ThomasRinsma/kb1/hardware/kb1.kicad_sch

## KiCad design hardware/kb1.kicad_sch (2024-02-07)

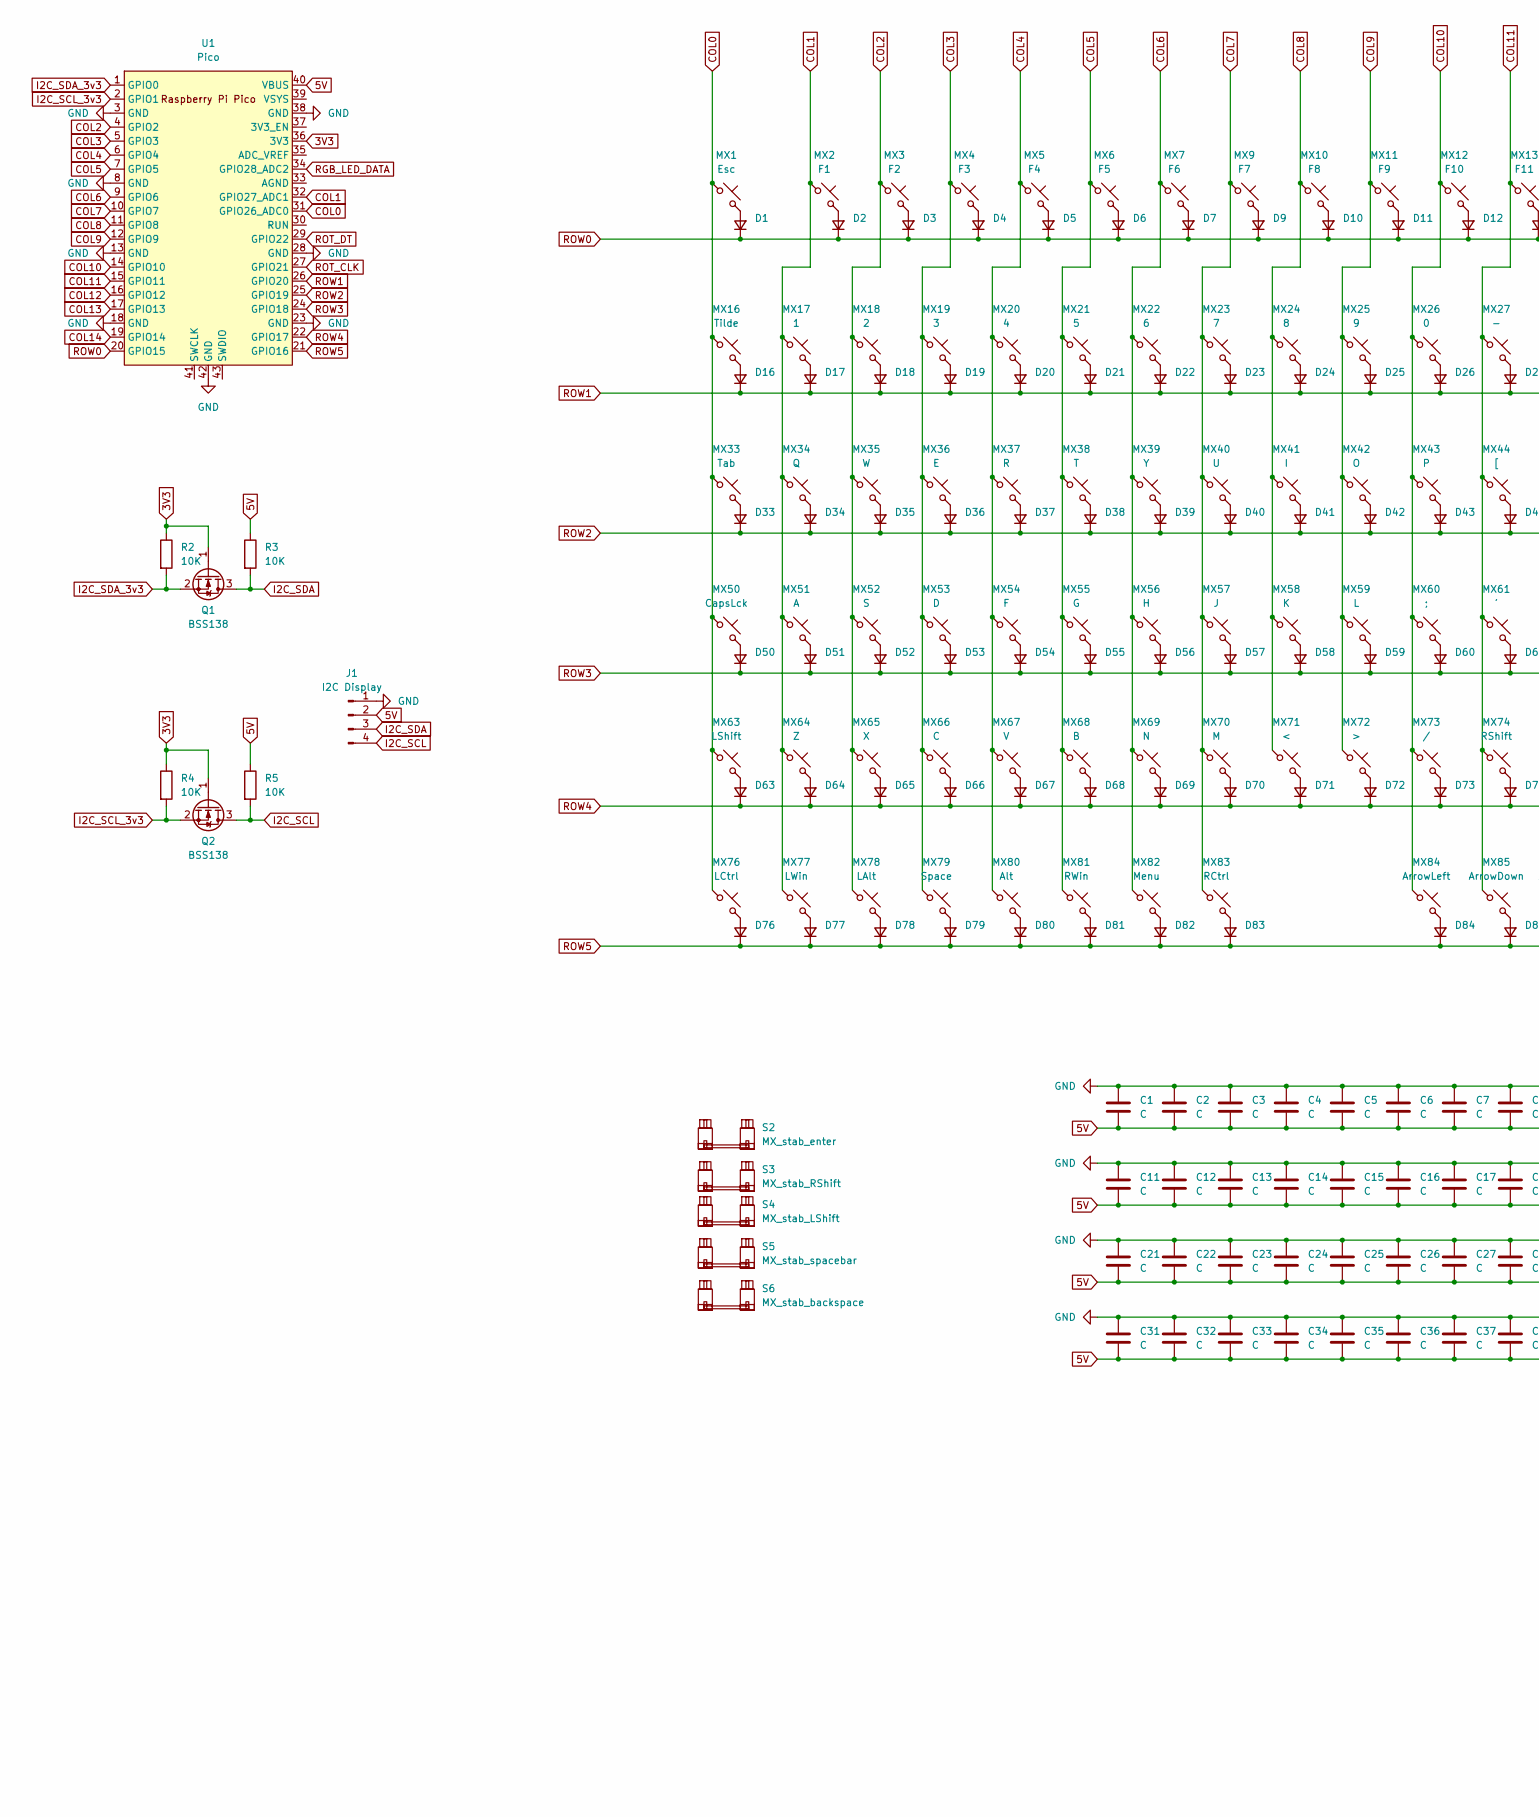
[picture p10: schematic kb1.kicad_sch, part in row 1, column 1]

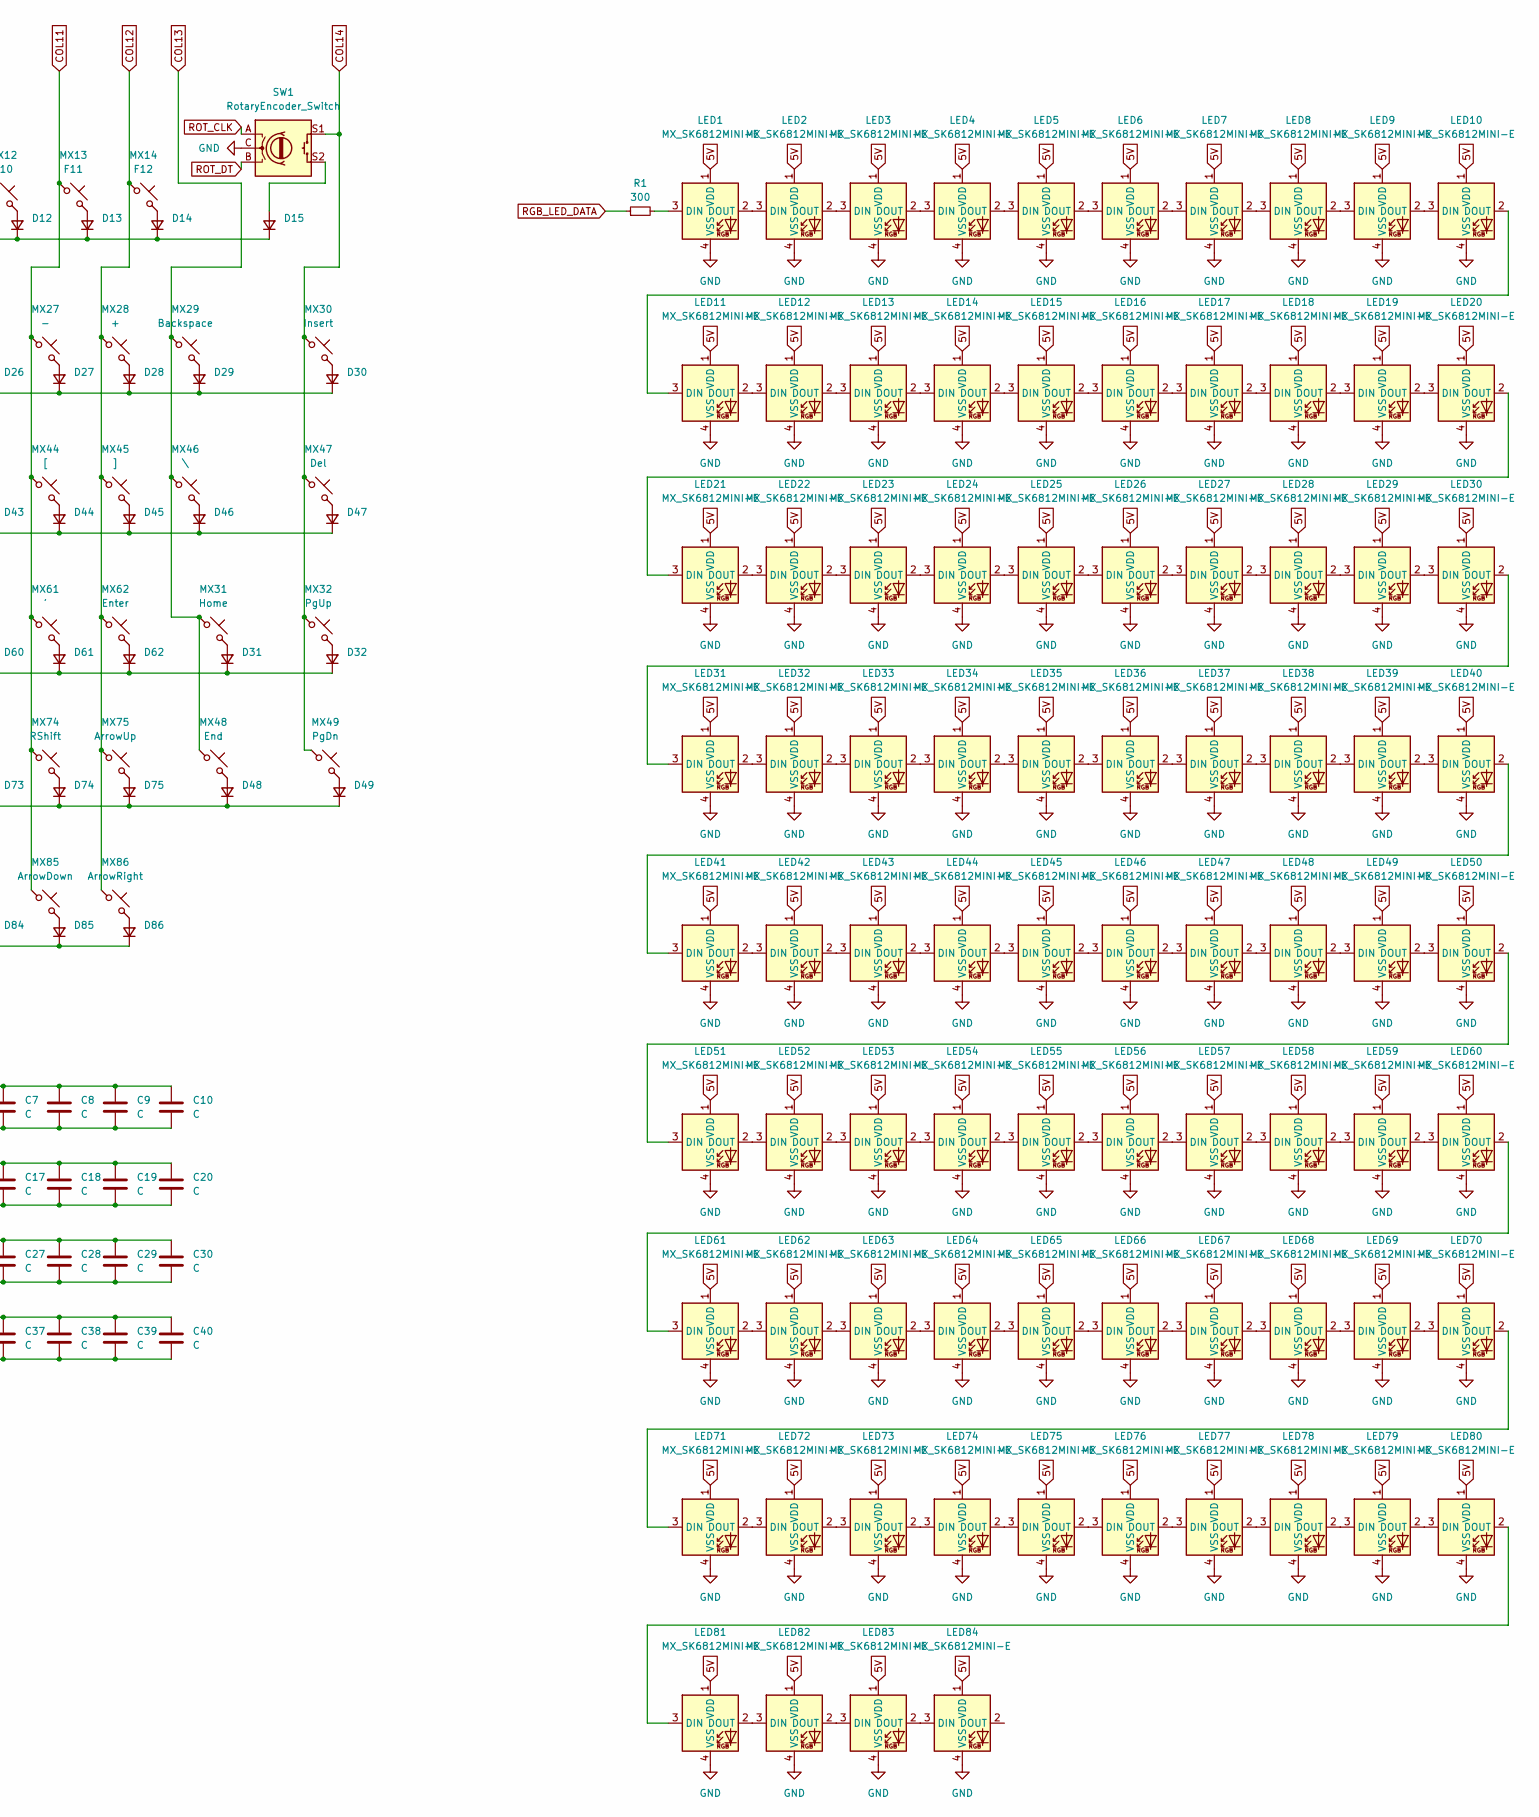
[picture p11: schematic kb1.kicad_sch, part in row 1, column 2]

Parts:
C1, C2, C3, C4, C5, C6, C7, C8, C9, C10, C11, C12, C13, C14, C15, C16, C17, C18, C19, C20, C21, C22, C23, C24, C25, C26, C27, C28, C29, C30, C31, C32, C33, C34, C35, C36, C37, C38, C39, C40: C; C_0805_2012Metric_Pad1.18x1.45mm_HandSolder
D1, D2, D3, D4, D5, D6, D7, D9, D10, D11, D12, D13, D14, D15, D16, D17, D18, D19, D20, D21, D22, D23, D24, D25, D26, D27, D28, D29, D30, D31, D32, D33, D34, D35, D36, D37, D38, D39, D40, D41, D42, D43, D44, D45, D46, D47, D48, D49, D50, D51, D52, D53, D54, D55, D56, D57, D58, D59, D60, D61, D62, D63, D64, D65, D66, D67, D68, D69, D70, D71, D72, D73, D74, D75, D76, D77, D78, D79, D80, D81, D82, D83, D84, D85, D86: D_SOD-123
J1: I2C Display; PinHeader_1x04_P2.54mm_Vertical
LED1, LED2, LED3, LED4, LED5, LED6, LED7, LED8, LED9, LED10, LED11, LED12, LED13, LED14, LED15, LED16, LED17, LED18, LED19, LED20, LED21, LED22, LED23, LED24, LED25, LED26, LED27, LED28, LED29, LED30, LED31, LED32, LED33, LED34, LED35, LED36, LED37, LED38, LED39, LED40, LED41, LED42, LED43, LED44, LED45, LED46, LED47, LED48, LED49, LED50, LED51, LED52, LED53, LED54, LED55, LED56, LED57, LED58, LED59, LED60, LED61, LED62, LED63, LED64, LED65, LED66, LED67, LED68, LED69, LED70, LED71, LED72, LED73, LED74, LED75, LED76, LED77, LED78, LED79, LED80, LED81, LED82, LED83, LED84: MX_SK6812MINI-E; LED_MX_6028R
MX1: Esc; SW_MX_1u
MX2: F1; SW_MX_1u
MX3: F2; SW_MX_1u
MX4: F3; SW_MX_1u
MX5: F4; SW_MX_1u
MX6: F5; SW_MX_1u
MX7: F6; SW_MX_1u
MX9: F7; SW_MX_1u
MX10: F8; SW_MX_1u
MX11: F9; SW_MX_1u
MX12: F10; SW_MX_1u
MX13: F11; SW_MX_1u
MX14: F12; SW_MX_1u
MX16: Tilde; SW_MX_1u
MX17: 1; SW_MX_1u
MX18: 2; SW_MX_1u
MX19: 3; SW_MX_1u
MX20: 4; SW_MX_1u
MX21: 5; SW_MX_1u
MX22: 6; SW_MX_1u
MX23: 7; SW_MX_1u
MX24: 8; SW_MX_1u
MX25: 9; SW_MX_1u
MX26: 0; SW_MX_1u
MX27: -; SW_MX_1u
MX28: +; SW_MX_1u
MX29: Backspace; SW_MX_1u
MX30: Insert; SW_MX_1u
MX31: Home; SW_MX_1u
MX32: PgUp; SW_MX_1u
MX33: Tab; SW_MX_1.5u
MX34: Q; SW_MX_1u
MX35: W; SW_MX_1u
MX36: E; SW_MX_1u
MX37: R; SW_MX_1u
MX38: T; SW_MX_1u
MX39: Y; SW_MX_1u
MX40: U; SW_MX_1u
MX41: I; SW_MX_1u
MX42: O; SW_MX_1u
MX43: P; SW_MX_1u
MX44: [; SW_MX_1u
MX45: ]; SW_MX_1u
MX46: \; SW_MX_1.5u
MX47: Del; SW_MX_1u
MX48: End; SW_MX_1u
MX49: PgDn; SW_MX_1u
MX50: CapsLck; SW_MX_1.75u
MX51: A; SW_MX_1u
MX52: S; SW_MX_1u
MX53: D; SW_MX_1u
MX54: F; SW_MX_1u
MX55: G; SW_MX_1u
MX56: H; SW_MX_1u
MX57: J; SW_MX_1u
MX58: K; SW_MX_1u
MX59: L; SW_MX_1u
MX60: ;; SW_MX_1u
MX61: '; SW_MX_1u
MX62: Enter; SW_MX_1u
MX63: LShift; SW_MX_1u
MX64: Z; SW_MX_1u
MX65: X; SW_MX_1u
MX66: C; SW_MX_1u
MX67: V; SW_MX_1u
MX68: B; SW_MX_1u
MX69: N; SW_MX_1u
MX70: M; SW_MX_1u
MX71: <; SW_MX_1u
MX72: >; SW_MX_1u
MX73: /; SW_MX_1u
MX74: RShift; SW_MX_1u
MX75: ArrowUp; SW_MX_1u
MX76: LCtrl; SW_MX_1.25u
MX77: LWin; SW_MX_1.25u
MX78: LAlt; SW_MX_1.25u
MX79: Space; SW_MX_1u
MX80: Alt; SW_MX_1.25u
MX81: RWin; SW_MX_1.25u
MX82: Menu; SW_MX_1.25u
MX83: RCtrl; SW_MX_1.25u
MX84: ArrowLeft; SW_MX_1u
MX85: ArrowDown; SW_MX_1u
MX86: ArrowRight; SW_MX_1u
Q1, Q2: BSS138; SOT-23
R1: 300; R_0805_2012Metric_Pad1.20x1.40mm_HandSolder
R2, R3, R4, R5: 10K; R_0805_2012Metric_Pad1.20x1.40mm_HandSolder
S2: MX_stab_enter; STAB_MX_P_2.25u
S3: MX_stab_RShift; STAB_MX_P_2.75u
S4: MX_stab_LShift; STAB_MX_P_2.25u
S5: MX_stab_spacebar; STAB_MX_P_6.25u
S6: MX_stab_backspace; STAB_MX_P_2u
SW1: RotaryEncoder_Switch; RotaryEncoder_Alps_EC11E-Switch_Vertical_H20mm
U1: Pico; RPi_Pico_SMD_TH

Connections:
3V3: Q1.1 (G), Q2.1 (G), R2.1, R4.1, U1.36 (3V3)
5V: C1.2, C2.2, C3.2, C4.2, C5.2, C6.2, C7.2, C8.2, C9.2, C10.2, C11.2, C12.2, C13.2, C14.2, C15.2, C16.2, C17.2, C18.2, C19.2, C20.2, C21.2, C22.2, C23.2, C24.2, C25.2, C26.2, C27.2, C28.2, C29.2, C30.2, C31.2, C32.2, C33.2, C34.2, C35.2, C36.2, C37.2, C38.2, C39.2, C40.2, J1.2, LED1.1 (VDD), LED2.1 (VDD), LED3.1 (VDD), LED4.1 (VDD), LED5.1 (VDD), LED6.1 (VDD), LED7.1 (VDD), LED8.1 (VDD), LED9.1 (VDD), LED10.1 (VDD), LED11.1 (VDD), LED12.1 (VDD), LED13.1 (VDD), LED14.1 (VDD), LED15.1 (VDD), LED16.1 (VDD), LED17.1 (VDD), LED18.1 (VDD), LED19.1 (VDD), LED20.1 (VDD), LED21.1 (VDD), LED22.1 (VDD), LED23.1 (VDD), LED24.1 (VDD), LED25.1 (VDD), LED26.1 (VDD), LED27.1 (VDD), LED28.1 (VDD), LED29.1 (VDD), LED30.1 (VDD), LED31.1 (VDD), LED32.1 (VDD), LED33.1 (VDD), LED34.1 (VDD), LED35.1 (VDD), LED36.1 (VDD), LED37.1 (VDD), LED38.1 (VDD), LED39.1 (VDD), LED40.1 (VDD), LED41.1 (VDD), LED42.1 (VDD), LED43.1 (VDD), LED44.1 (VDD), LED45.1 (VDD), LED46.1 (VDD), LED47.1 (VDD), LED48.1 (VDD), LED49.1 (VDD), LED50.1 (VDD), LED51.1 (VDD), LED52.1 (VDD), LED53.1 (VDD), LED54.1 (VDD), LED55.1 (VDD), LED56.1 (VDD), LED57.1 (VDD), LED58.1 (VDD), LED59.1 (VDD), LED60.1 (VDD), LED61.1 (VDD), LED62.1 (VDD), LED63.1 (VDD), LED64.1 (VDD), LED65.1 (VDD), LED66.1 (VDD), LED67.1 (VDD), LED68.1 (VDD), LED69.1 (VDD), LED70.1 (VDD), LED71.1 (VDD), LED72.1 (VDD), LED73.1 (VDD), LED74.1 (VDD), LED75.1 (VDD), LED76.1 (VDD), LED77.1 (VDD), LED78.1 (VDD), LED79.1 (VDD), LED80.1 (VDD), LED81.1 (VDD), LED82.1 (VDD), LED83.1 (VDD), LED84.1 (VDD), R3.1, R5.1, U1.40 (VBUS)
COL0: MX1.1, MX16.1, MX33.1, MX50.1, MX63.1, MX76.1, U1.31 (GPIO26_ADC0)
COL1: MX2.1, MX17.1, MX34.1, MX51.1, MX64.1, MX77.1, U1.32 (GPIO27_ADC1)
COL2: MX3.1, MX18.1, MX35.1, MX52.1, MX65.1, MX78.1, U1.4 (GPIO2)
COL3: MX4.1, MX19.1, MX36.1, MX53.1, MX66.1, MX79.1, U1.5 (GPIO3)
COL4: MX5.1, MX20.1, MX37.1, MX54.1, MX67.1, MX80.1, U1.6 (GPIO4)
COL5: MX6.1, MX21.1, MX38.1, MX55.1, MX68.1, MX81.1, U1.7 (GPIO5)
COL6: MX7.1, MX22.1, MX39.1, MX56.1, MX69.1, MX82.1, U1.9 (GPIO6)
COL7: MX9.1, MX23.1, MX40.1, MX57.1, MX70.1, MX83.1, U1.10 (GPIO7)
COL8: MX10.1, MX24.1, MX41.1, MX58.1, MX71.1, U1.11 (GPIO8)
COL9: MX11.1, MX25.1, MX42.1, MX59.1, MX72.1, U1.12 (GPIO9)
COL10: MX12.1, MX26.1, MX43.1, MX60.1, MX73.1, MX84.1, U1.14 (GPIO10)
COL11: MX13.1, MX27.1, MX44.1, MX61.1, MX74.1, MX85.1, U1.15 (GPIO11)
COL12: MX14.1, MX28.1, MX45.1, MX62.1, MX75.1, MX86.1, U1.16 (GPIO12)
COL13: MX29.1, MX31.1, MX46.1, MX48.1, U1.17 (GPIO13)
COL14: MX30.1, MX32.1, MX47.1, MX49.1, SW1.S1, U1.19 (GPIO14)
GND: C1.1, C2.1, C3.1, C4.1, C5.1, C6.1, C7.1, C8.1, C9.1, C10.1, C11.1, C12.1, C13.1, C14.1, C15.1, C16.1, C17.1, C18.1, C19.1, C20.1, C21.1, C22.1, C23.1, C24.1, C25.1, C26.1, C27.1, C28.1, C29.1, C30.1, C31.1, C32.1, C33.1, C34.1, C35.1, C36.1, C37.1, C38.1, C39.1, C40.1, J1.1, LED1.4 (VSS), LED2.4 (VSS), LED3.4 (VSS), LED4.4 (VSS), LED5.4 (VSS), LED6.4 (VSS), LED7.4 (VSS), LED8.4 (VSS), LED9.4 (VSS), LED10.4 (VSS), LED11.4 (VSS), LED12.4 (VSS), LED13.4 (VSS), LED14.4 (VSS), LED15.4 (VSS), LED16.4 (VSS), LED17.4 (VSS), LED18.4 (VSS), LED19.4 (VSS), LED20.4 (VSS), LED21.4 (VSS), LED22.4 (VSS), LED23.4 (VSS), LED24.4 (VSS), LED25.4 (VSS), LED26.4 (VSS), LED27.4 (VSS), LED28.4 (VSS), LED29.4 (VSS), LED30.4 (VSS), LED31.4 (VSS), LED32.4 (VSS), LED33.4 (VSS), LED34.4 (VSS), LED35.4 (VSS), LED36.4 (VSS), LED37.4 (VSS), LED38.4 (VSS), LED39.4 (VSS), LED40.4 (VSS), LED41.4 (VSS), LED42.4 (VSS), LED43.4 (VSS), LED44.4 (VSS), LED45.4 (VSS), LED46.4 (VSS), LED47.4 (VSS), LED48.4 (VSS), LED49.4 (VSS), LED50.4 (VSS), LED51.4 (VSS), LED52.4 (VSS), LED53.4 (VSS), LED54.4 (VSS), LED55.4 (VSS), LED56.4 (VSS), LED57.4 (VSS), LED58.4 (VSS), LED59.4 (VSS), LED60.4 (VSS), LED61.4 (VSS), LED62.4 (VSS), LED63.4 (VSS), LED64.4 (VSS), LED65.4 (VSS), LED66.4 (VSS), LED67.4 (VSS), LED68.4 (VSS), LED69.4 (VSS), LED70.4 (VSS), LED71.4 (VSS), LED72.4 (VSS), LED73.4 (VSS), LED74.4 (VSS), LED75.4 (VSS), LED76.4 (VSS), LED77.4 (VSS), LED78.4 (VSS), LED79.4 (VSS), LED80.4 (VSS), LED81.4 (VSS), LED82.4 (VSS), LED83.4 (VSS), LED84.4 (VSS), SW1.C, U1.3 (GND), U1.8 (GND), U1.13 (GND), U1.18 (GND), U1.23 (GND), U1.28 (GND), U1.38 (GND), U1.42 (GND)
I2C_SCL: J1.4, Q2.3 (D), R5.2
I2C_SCL_3v3: Q2.2 (S), R4.2, U1.2 (GPIO1)
I2C_SDA: J1.3, Q1.3 (D), R3.2
I2C_SDA_3v3: Q1.2 (S), R2.2, U1.1 (GPIO0)
unnamed: D1.2 (A), MX1.2
unnamed: D2.2 (A), MX2.2
unnamed: D3.2 (A), MX3.2
unnamed: D4.2 (A), MX4.2
unnamed: D5.2 (A), MX5.2
unnamed: D6.2 (A), MX6.2
unnamed: D7.2 (A), MX7.2
unnamed: D9.2 (A), MX9.2
unnamed: D10.2 (A), MX10.2
unnamed: D11.2 (A), MX11.2
unnamed: D12.2 (A), MX12.2
unnamed: D13.2 (A), MX13.2
unnamed: D14.2 (A), MX14.2
unnamed: D15.2 (A), SW1.S2
unnamed: D16.2 (A), MX16.2
unnamed: D17.2 (A), MX17.2
unnamed: D18.2 (A), MX18.2
unnamed: D19.2 (A), MX19.2
unnamed: D20.2 (A), MX20.2
unnamed: D21.2 (A), MX21.2
unnamed: D22.2 (A), MX22.2
unnamed: D23.2 (A), MX23.2
unnamed: D24.2 (A), MX24.2
unnamed: D25.2 (A), MX25.2
unnamed: D26.2 (A), MX26.2
unnamed: D27.2 (A), MX27.2
unnamed: D28.2 (A), MX28.2
unnamed: D29.2 (A), MX29.2
unnamed: D30.2 (A), MX30.2
unnamed: D31.2 (A), MX31.2
unnamed: D32.2 (A), MX32.2
unnamed: D33.2 (A), MX33.2
unnamed: D34.2 (A), MX34.2
unnamed: D35.2 (A), MX35.2
unnamed: D36.2 (A), MX36.2
unnamed: D37.2 (A), MX37.2
unnamed: D38.2 (A), MX38.2
unnamed: D39.2 (A), MX39.2
unnamed: D40.2 (A), MX40.2
unnamed: D41.2 (A), MX41.2
unnamed: D42.2 (A), MX42.2
unnamed: D43.2 (A), MX43.2
unnamed: D44.2 (A), MX44.2
unnamed: D45.2 (A), MX45.2
unnamed: D46.2 (A), MX46.2
unnamed: D47.2 (A), MX47.2
unnamed: D48.2 (A), MX48.2
unnamed: D49.2 (A), MX49.2
unnamed: D50.2 (A), MX50.2
unnamed: D51.2 (A), MX51.2
unnamed: D52.2 (A), MX52.2
unnamed: D53.2 (A), MX53.2
unnamed: D54.2 (A), MX54.2
unnamed: D55.2 (A), MX55.2
unnamed: D56.2 (A), MX56.2
unnamed: D57.2 (A), MX57.2
unnamed: D58.2 (A), MX58.2
unnamed: D59.2 (A), MX59.2
unnamed: D60.2 (A), MX60.2
unnamed: D61.2 (A), MX61.2
unnamed: D62.2 (A), MX62.2
unnamed: D63.2 (A), MX63.2
unnamed: D64.2 (A), MX64.2
unnamed: D65.2 (A), MX65.2
unnamed: D66.2 (A), MX66.2
unnamed: D67.2 (A), MX67.2
unnamed: D68.2 (A), MX68.2
unnamed: D69.2 (A), MX69.2
unnamed: D70.2 (A), MX70.2
unnamed: D71.2 (A), MX71.2
unnamed: D72.2 (A), MX72.2
unnamed: D73.2 (A), MX73.2
unnamed: D74.2 (A), MX74.2
unnamed: D75.2 (A), MX75.2
unnamed: D76.2 (A), MX76.2
unnamed: D77.2 (A), MX77.2
unnamed: D78.2 (A), MX78.2
unnamed: D79.2 (A), MX79.2
unnamed: D80.2 (A), MX80.2
unnamed: D81.2 (A), MX81.2
unnamed: D82.2 (A), MX82.2
unnamed: D83.2 (A), MX83.2
unnamed: D84.2 (A), MX84.2
unnamed: D85.2 (A), MX85.2
unnamed: D86.2 (A), MX86.2
unnamed: LED1.2 (DOUT), LED2.3 (DIN)
unnamed: LED1.3 (DIN), R1.2
unnamed: LED2.2 (DOUT), LED3.3 (DIN)
unnamed: LED3.2 (DOUT), LED4.3 (DIN)
unnamed: LED4.2 (DOUT), LED5.3 (DIN)
unnamed: LED5.2 (DOUT), LED6.3 (DIN)
unnamed: LED6.2 (DOUT), LED7.3 (DIN)
unnamed: LED7.2 (DOUT), LED8.3 (DIN)
unnamed: LED8.2 (DOUT), LED9.3 (DIN)
unnamed: LED10.2 (DOUT), LED11.3 (DIN)
unnamed: LED9.2 (DOUT), LED10.3 (DIN)
unnamed: LED11.2 (DOUT), LED12.3 (DIN)
unnamed: LED12.2 (DOUT), LED13.3 (DIN)
unnamed: LED13.2 (DOUT), LED14.3 (DIN)
unnamed: LED14.2 (DOUT), LED15.3 (DIN)
unnamed: LED15.2 (DOUT), LED16.3 (DIN)
unnamed: LED16.2 (DOUT), LED17.3 (DIN)
unnamed: LED17.2 (DOUT), LED18.3 (DIN)
unnamed: LED18.2 (DOUT), LED19.3 (DIN)
unnamed: LED19.2 (DOUT), LED20.3 (DIN)
unnamed: LED20.2 (DOUT), LED21.3 (DIN)
unnamed: LED21.2 (DOUT), LED22.3 (DIN)
unnamed: LED22.2 (DOUT), LED23.3 (DIN)
unnamed: LED23.2 (DOUT), LED24.3 (DIN)
unnamed: LED24.2 (DOUT), LED25.3 (DIN)
unnamed: LED25.2 (DOUT), LED26.3 (DIN)
unnamed: LED26.2 (DOUT), LED27.3 (DIN)
unnamed: LED27.2 (DOUT), LED28.3 (DIN)
unnamed: LED28.2 (DOUT), LED29.3 (DIN)
unnamed: LED29.2 (DOUT), LED30.3 (DIN)
unnamed: LED30.2 (DOUT), LED31.3 (DIN)
unnamed: LED31.2 (DOUT), LED32.3 (DIN)
unnamed: LED32.2 (DOUT), LED33.3 (DIN)
unnamed: LED33.2 (DOUT), LED34.3 (DIN)
unnamed: LED34.2 (DOUT), LED35.3 (DIN)
unnamed: LED35.2 (DOUT), LED36.3 (DIN)
unnamed: LED36.2 (DOUT), LED37.3 (DIN)
unnamed: LED37.2 (DOUT), LED38.3 (DIN)
unnamed: LED38.2 (DOUT), LED39.3 (DIN)
unnamed: LED39.2 (DOUT), LED40.3 (DIN)
unnamed: LED40.2 (DOUT), LED41.3 (DIN)
unnamed: LED41.2 (DOUT), LED42.3 (DIN)
unnamed: LED42.2 (DOUT), LED43.3 (DIN)
unnamed: LED43.2 (DOUT), LED44.3 (DIN)
unnamed: LED44.2 (DOUT), LED45.3 (DIN)
unnamed: LED45.2 (DOUT), LED46.3 (DIN)
unnamed: LED46.2 (DOUT), LED47.3 (DIN)
unnamed: LED47.2 (DOUT), LED48.3 (DIN)
unnamed: LED48.2 (DOUT), LED49.3 (DIN)
unnamed: LED49.2 (DOUT), LED50.3 (DIN)
unnamed: LED50.2 (DOUT), LED51.3 (DIN)
unnamed: LED51.2 (DOUT), LED52.3 (DIN)
unnamed: LED52.2 (DOUT), LED53.3 (DIN)
unnamed: LED53.2 (DOUT), LED54.3 (DIN)
unnamed: LED54.2 (DOUT), LED55.3 (DIN)
unnamed: LED55.2 (DOUT), LED56.3 (DIN)
unnamed: LED56.2 (DOUT), LED57.3 (DIN)
unnamed: LED57.2 (DOUT), LED58.3 (DIN)
unnamed: LED58.2 (DOUT), LED59.3 (DIN)
unnamed: LED59.2 (DOUT), LED60.3 (DIN)
unnamed: LED60.2 (DOUT), LED61.3 (DIN)
unnamed: LED61.2 (DOUT), LED62.3 (DIN)
unnamed: LED62.2 (DOUT), LED63.3 (DIN)
unnamed: LED63.2 (DOUT), LED64.3 (DIN)
unnamed: LED64.2 (DOUT), LED65.3 (DIN)
unnamed: LED65.2 (DOUT), LED66.3 (DIN)
unnamed: LED66.2 (DOUT), LED67.3 (DIN)
unnamed: LED67.2 (DOUT), LED68.3 (DIN)
unnamed: LED68.2 (DOUT), LED69.3 (DIN)
unnamed: LED69.2 (DOUT), LED70.3 (DIN)
unnamed: LED70.2 (DOUT), LED71.3 (DIN)
unnamed: LED71.2 (DOUT), LED72.3 (DIN)
unnamed: LED72.2 (DOUT), LED73.3 (DIN)
unnamed: LED73.2 (DOUT), LED74.3 (DIN)
unnamed: LED74.2 (DOUT), LED75.3 (DIN)
unnamed: LED75.2 (DOUT), LED76.3 (DIN)
unnamed: LED76.2 (DOUT), LED77.3 (DIN)
unnamed: LED77.2 (DOUT), LED78.3 (DIN)
unnamed: LED78.2 (DOUT), LED79.3 (DIN)
unnamed: LED79.2 (DOUT), LED80.3 (DIN)
unnamed: LED80.2 (DOUT), LED81.3 (DIN)
unnamed: LED81.2 (DOUT), LED82.3 (DIN)
unnamed: LED82.2 (DOUT), LED83.3 (DIN)
unnamed: LED83.2 (DOUT), LED84.3 (DIN)
RGB_LED_DATA: R1.1, U1.34 (GPIO28_ADC2)
ROT_CLK: SW1.A, U1.27 (GPIO21)
ROT_DT: SW1.B, U1.29 (GPIO22)
ROW0: D1.1 (K), D2.1 (K), D3.1 (K), D4.1 (K), D5.1 (K), D6.1 (K), D7.1 (K), D9.1 (K), D10.1 (K), D11.1 (K), D12.1 (K), D13.1 (K), D14.1 (K), D15.1 (K), U1.20 (GPIO15)
ROW1: D16.1 (K), D17.1 (K), D18.1 (K), D19.1 (K), D20.1 (K), D21.1 (K), D22.1 (K), D23.1 (K), D24.1 (K), D25.1 (K), D26.1 (K), D27.1 (K), D28.1 (K), D29.1 (K), D30.1 (K), U1.26 (GPIO20)
ROW2: D33.1 (K), D34.1 (K), D35.1 (K), D36.1 (K), D37.1 (K), D38.1 (K), D39.1 (K), D40.1 (K), D41.1 (K), D42.1 (K), D43.1 (K), D44.1 (K), D45.1 (K), D46.1 (K), D47.1 (K), U1.25 (GPIO19)
ROW3: D31.1 (K), D32.1 (K), D50.1 (K), D51.1 (K), D52.1 (K), D53.1 (K), D54.1 (K), D55.1 (K), D56.1 (K), D57.1 (K), D58.1 (K), D59.1 (K), D60.1 (K), D61.1 (K), D62.1 (K), U1.24 (GPIO18)
ROW4: D48.1 (K), D49.1 (K), D63.1 (K), D64.1 (K), D65.1 (K), D66.1 (K), D67.1 (K), D68.1 (K), D69.1 (K), D70.1 (K), D71.1 (K), D72.1 (K), D73.1 (K), D74.1 (K), D75.1 (K), U1.22 (GPIO17)
ROW5: D76.1 (K), D77.1 (K), D78.1 (K), D79.1 (K), D80.1 (K), D81.1 (K), D82.1 (K), D83.1 (K), D84.1 (K), D85.1 (K), D86.1 (K), U1.21 (GPIO16)
